HenraL/bloated_mp3_player/bonus/rta/assets/gantt_edf.png

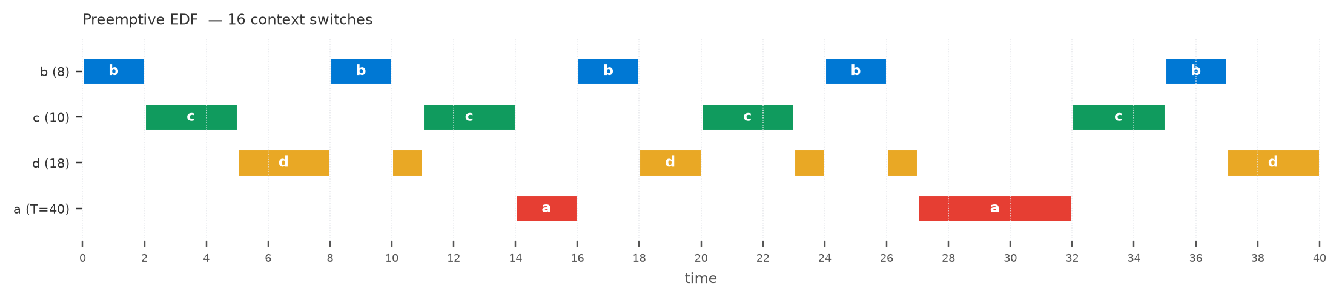
bonus/rta/assets/gantt_edf.png
