HenraL/bloated_mp3_player/bonus/rta/assets/gantt_edf_np.png

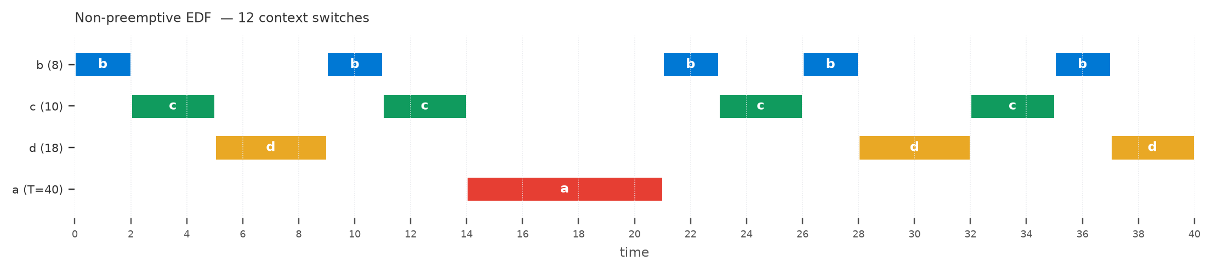
bonus/rta/assets/gantt_edf_np.png
