HenraL/bloated_mp3_player/bonus/rta/assets/gantt_rm.png

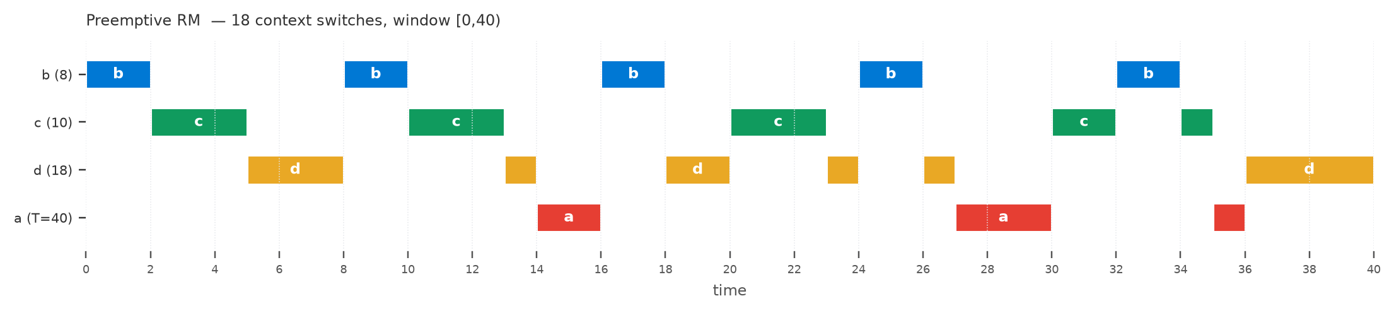
bonus/rta/assets/gantt_rm.png
