HenraL/bloated_mp3_player/kicad/export/mp3_player.svg/lcd_region.png

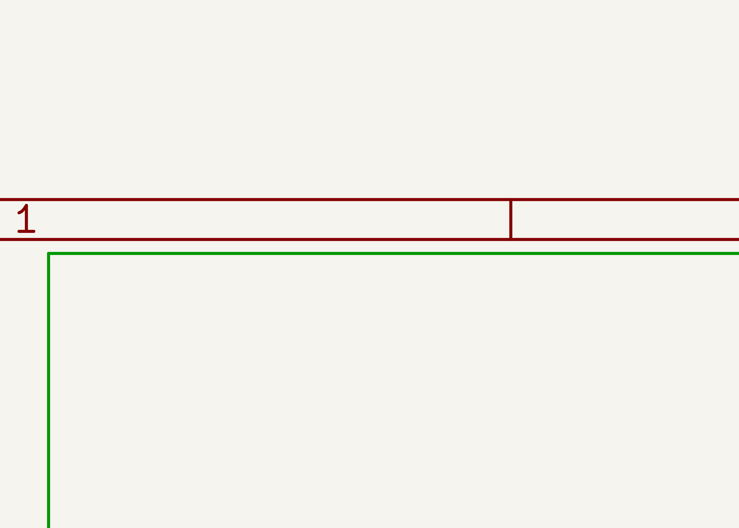
kicad/export/mp3_player.svg/lcd_region.png
