HenraL/bloated_mp3_player/kicad/export/mp3_player.svg/mp3_player.png

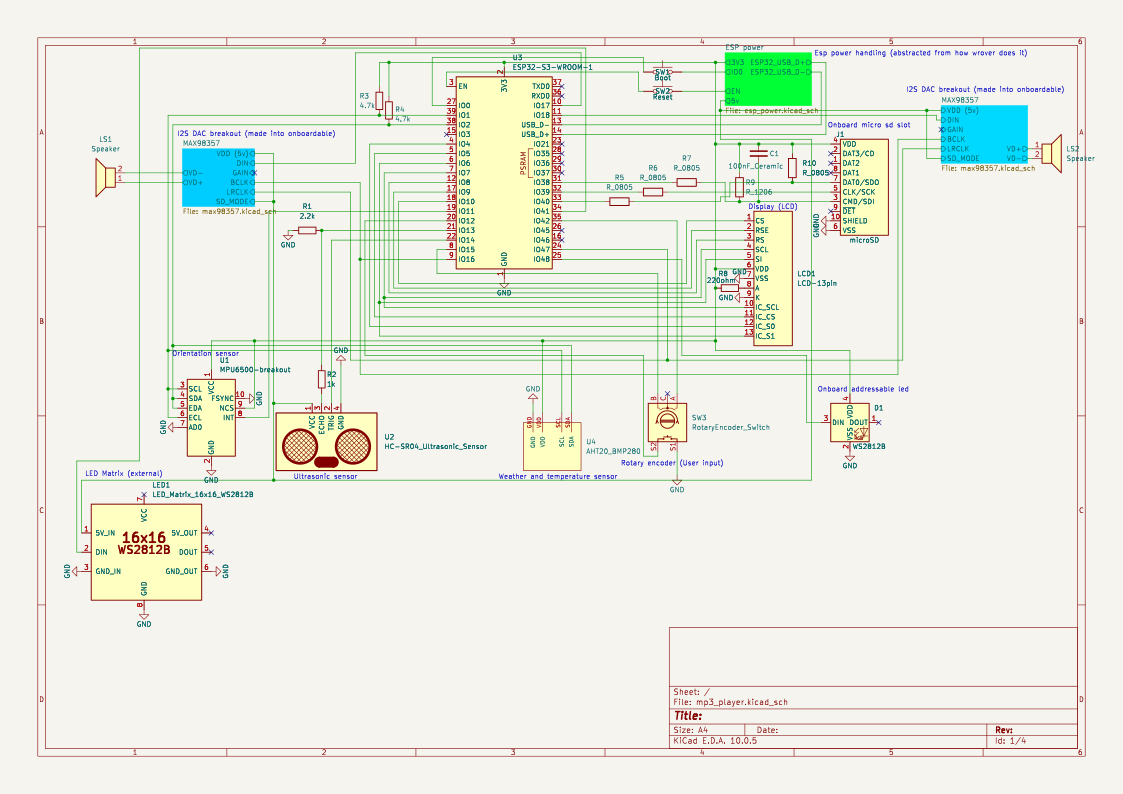
kicad/export/mp3_player.svg/mp3_player.png
