HenraL/bloated_mp3_player/platformio/bloated_mp3_player/include/my/config/delays.hpp

/*
* +==== BEGIN Bloated MP3 Player =================+
* LOGO:
* .......................
* ...><>.............<><.
* ..><>.><>.......<><.<><
* .><>.<><.><>.<><.<><.<>
* ..><>.><>.......<><.<><
* ...><>.............<><.
* .......................
* /STOP
* PROJECT: Bloated MP3 Player
* FILE: delays.hpp
* CREATION DATE: 20-07-2026
* LAST Modified: 17:47:30 31-07-2026
* DESCRIPTION:
* This is the code in charge of making the bloated player come to life.
* /STOP
* COPYRIGHT: (c) Henry Letellier
* PURPOSE: This is the file that will contain the imposed delays required during initialisation and runtime.
* // AR
* +==== END Bloated MP3 Player =================+
*/
#pragma once
#include <stdint.h>

namespace My
{
    namespace Config
    {
        namespace Delays
        {
            // Initialisation delay for the serial instance (as well as for the dev to connect to the serial output)
            static const uint32_t SERIAL_INITIALISATION_DELAY = 500; //ms
            static const uint32_t PRE_THREAD_INITIALISATION_DELAY = 1000; //ms

            // How often to poll the AHT20+BMP280 environmental sensor (milliseconds)
            static const uint32_t ENVIRONMENTAL_POLL_INTERVAL_MS = 5000; //ms

            // Wire.setTimeout() value: bounds how long a single I2C transaction
            // may stall (e.g. a missing device holding SCL) before aborted.
            // 0 = no timeout (default). Small values unstick a hung bus.
            static const uint32_t I2C_TRANSACTION_TIMEOUT_MS = 50; //ms

            // Environemental sensor initialisation issue, delay so the message can be read
            static const uint32_t ENVIRONMENTAL_INITIALISATION_ISSUE_MS = 5000; //ms

            // IMU initialisation issue, delay so the message can be read
            static const uint32_t IMU_INITIALISATION_FAILURE_MS = 5000; //ms

            // No sd card, delay so the message can be read
            static const uint32_t SD_CARD_NOT_PRESENT_MESSAGE_MS = 5000; //ms

            // No tracks, delay so the message can be read
            static const uint32_t SD_CARD_NO_MUSIC_PRESENT_MS = 5000; //ms

            // Audio channel handler initialisation issue, delay so the message can be read.
            static const uint32_t AUDIO_HANDLER_I2S_OPEN_FAILURE_MS = 5000; //ms
        } // namespace Delays
    } // namespace Config
} // namespace My
